jcorcoran/Kia_Niro_VESS_Mod/img/IMG_20220522_115506.jpg

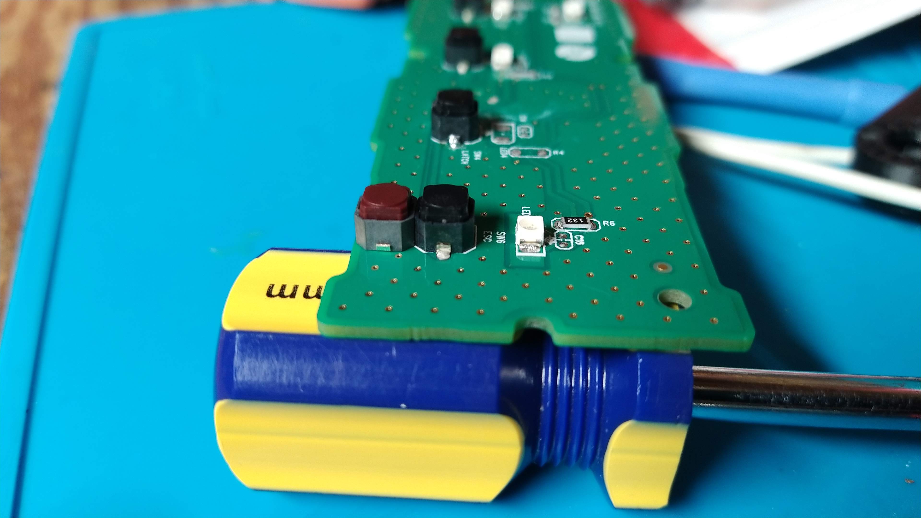
img/IMG_20220522_115506.jpg
