jcorcoran/Kia_Niro_VESS_Mod/img/IMG_20220522_120012.jpg

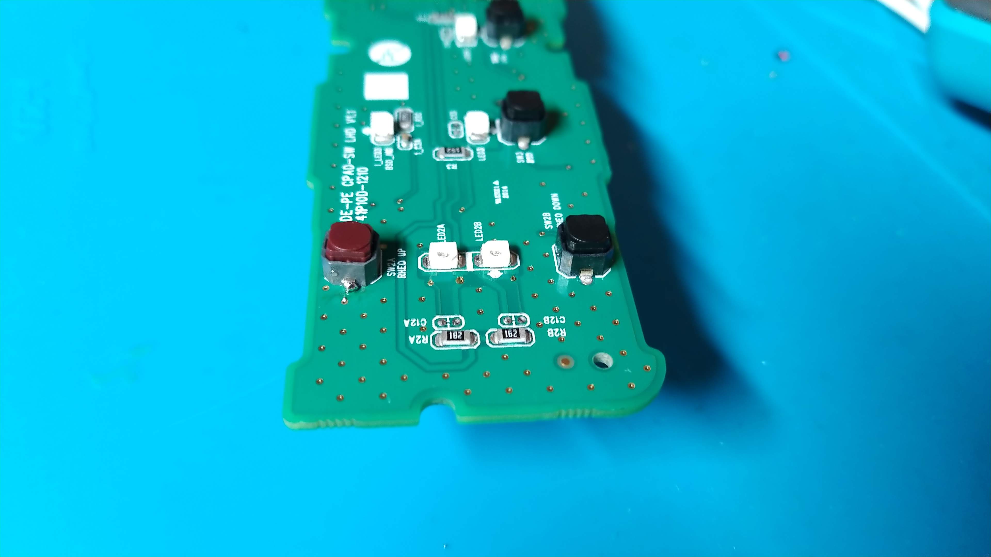
img/IMG_20220522_120012.jpg
